nilaymastaadmi/rv32-dsp-soc/hardware/uart-usb-breakout/uart-usb-breakout.kicad_sch

## KiCad design hardware/uart-usb-breakout/uart-usb-breakout.kicad_sch (2026-07-27)

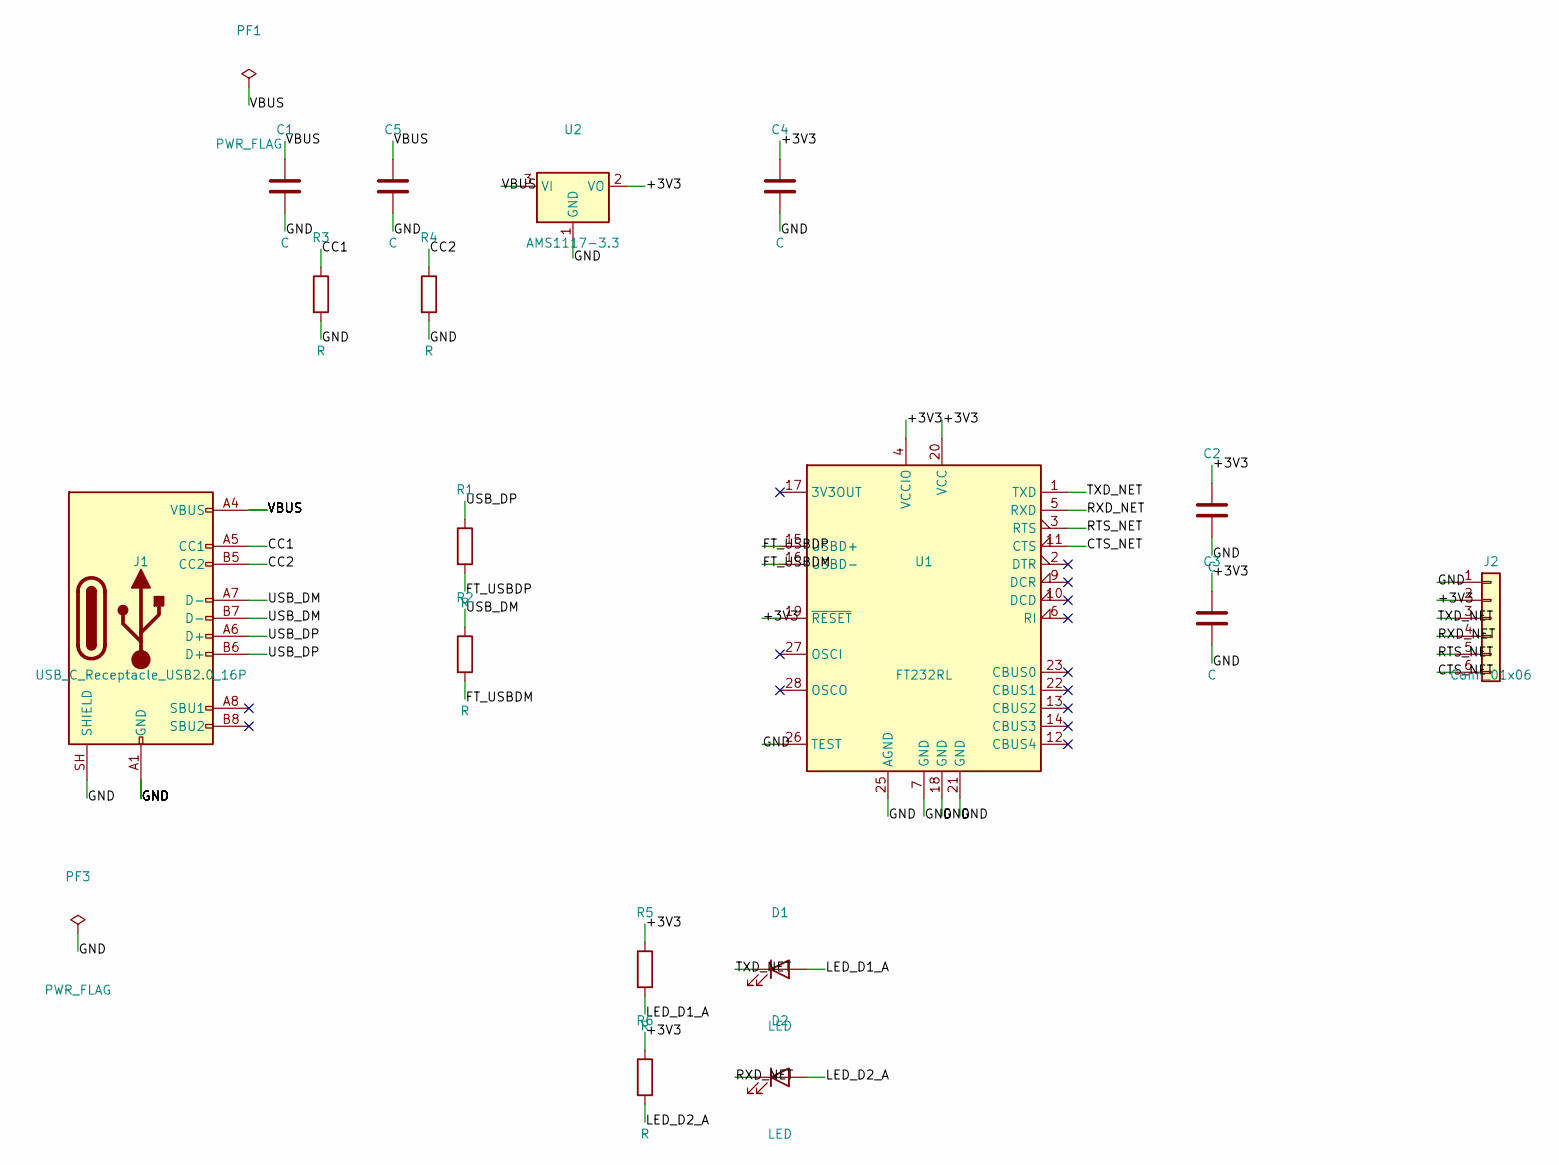
[picture p2: schematic uart-usb-breakout.kicad_sch]

Parts:
C1, C2, C3, C4, C5: C
D1, D2: LED
J1: USB_C_Receptacle_USB2.0_16P
J2: Conn_01x06
PF1, PF3: PWR_FLAG
R1, R2, R3, R4, R5, R6: R
U1: FT232RL
U2: AMS1117-3.3

Connections:
+3V3: C2.1, C3.1, C4.1, J2.2, R5.1, R6.1, U1.4 (VCCIO), U1.19 (~RESET), U1.20 (VCC), U2.2 (VO)
CC1: J1.A5 (CC1), R3.1
CC2: J1.B5 (CC2), R4.1
CTS_NET: J2.6, U1.11 (CTS)
FT_USBDM: R2.2, U1.16 (USBD-)
FT_USBDP: R1.2, U1.15 (USBD+)
GND: C1.2, C2.2, C3.2, C4.2, C5.2, J1.A1 (GND), J1.A12 (GND), J1.B1 (GND), J1.B12 (GND), J1.SH (SHIELD), J2.1, PF3.1, R3.2, R4.2, U1.7 (GND), U1.18 (GND), U1.21 (GND), U1.25 (AGND), U1.26 (TEST), U2.1 (GND)
LED_D1_A: D1.2 (A), R5.2
LED_D2_A: D2.2 (A), R6.2
RTS_NET: J2.5, U1.3 (RTS)
RXD_NET: D2.1 (K), J2.4, U1.5 (RXD)
TXD_NET: D1.1 (K), J2.3, U1.1 (TXD)
USB_DM: J1.A7 (D-), J1.B7 (D-), R2.1
USB_DP: J1.A6 (D+), J1.B6 (D+), R1.1
VBUS: C1.1, C5.1, J1.A4 (VBUS), J1.A9 (VBUS), J1.B4 (VBUS), J1.B9 (VBUS), PF1.1, U2.3 (VI)
